ak66666/ThumbsUpUnsplitV9/Photos/IMG_20240110_212607524.jpg

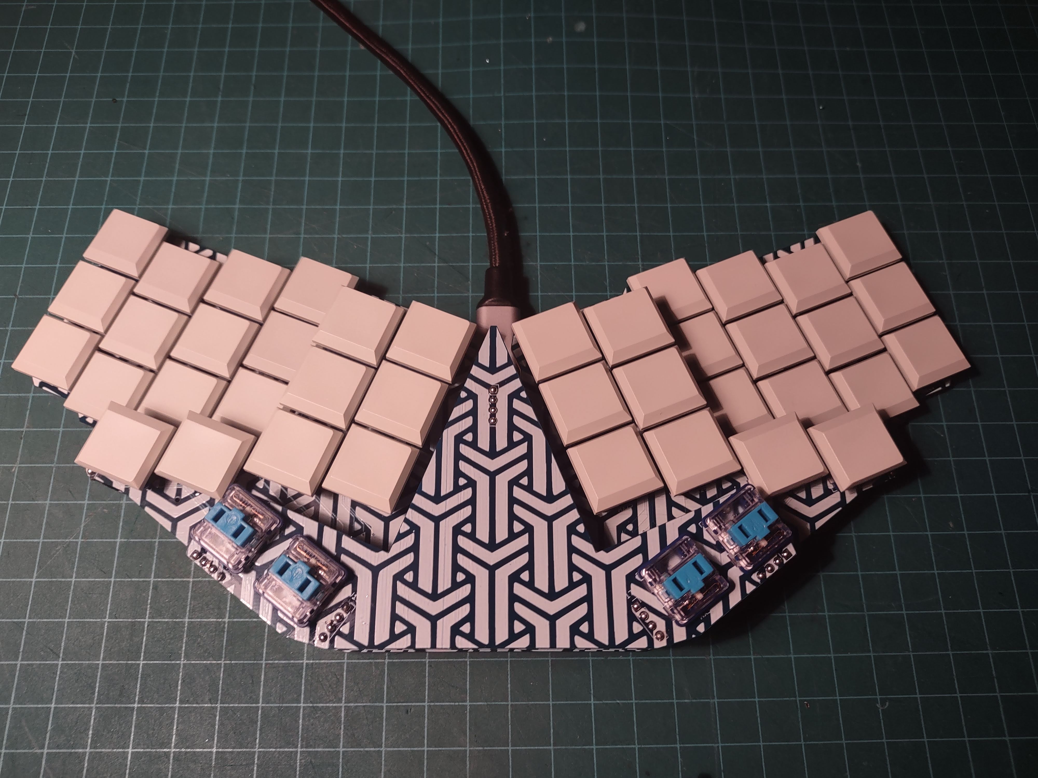
Photos/IMG_20240110_212607524.jpg
