ak66666/ThumbsUpUnsplitV9/Photos/IMG_20240110_212735549.jpg

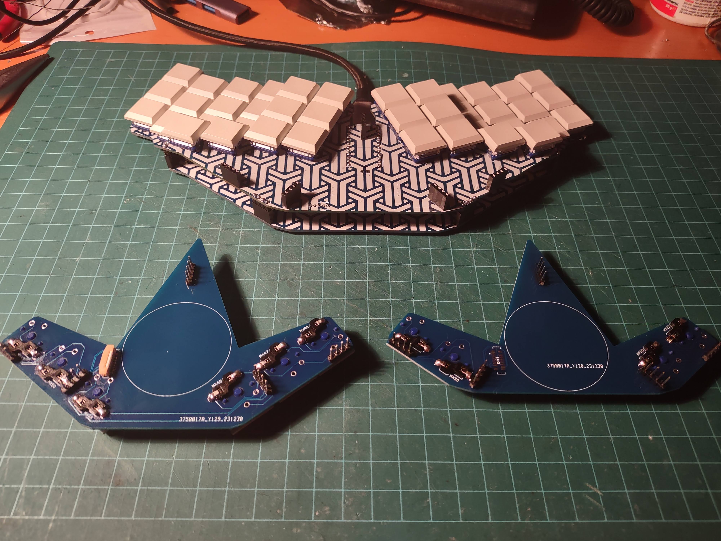
Photos/IMG_20240110_212735549.jpg
