ak66666/ThumbsUpUnsplitV9/Photos/IMG_20240110_212812123_HDR.jpg

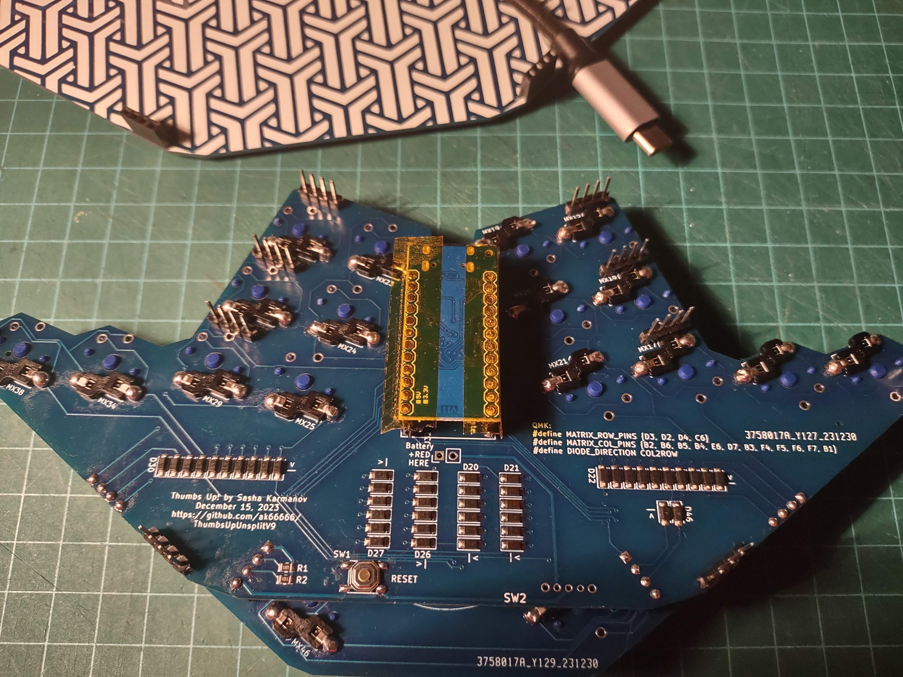
Photos/IMG_20240110_212812123_HDR.jpg
