ak66666/ThumbsUpUnsplitV9/Photos/IMG_20240110_213109584_HDR.jpg

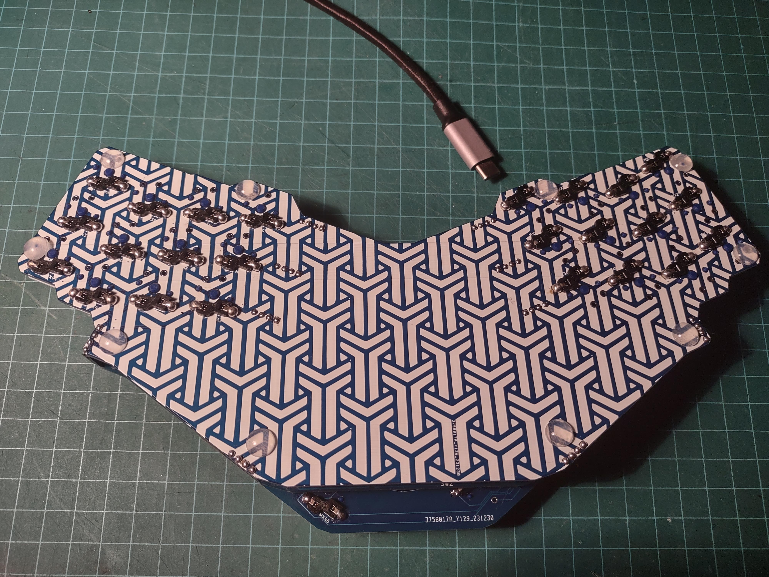
Photos/IMG_20240110_213109584_HDR.jpg
