ak66666/ThumbsUpUnsplitV9/Photos/IMG_20240401_145029431_HDR.jpg

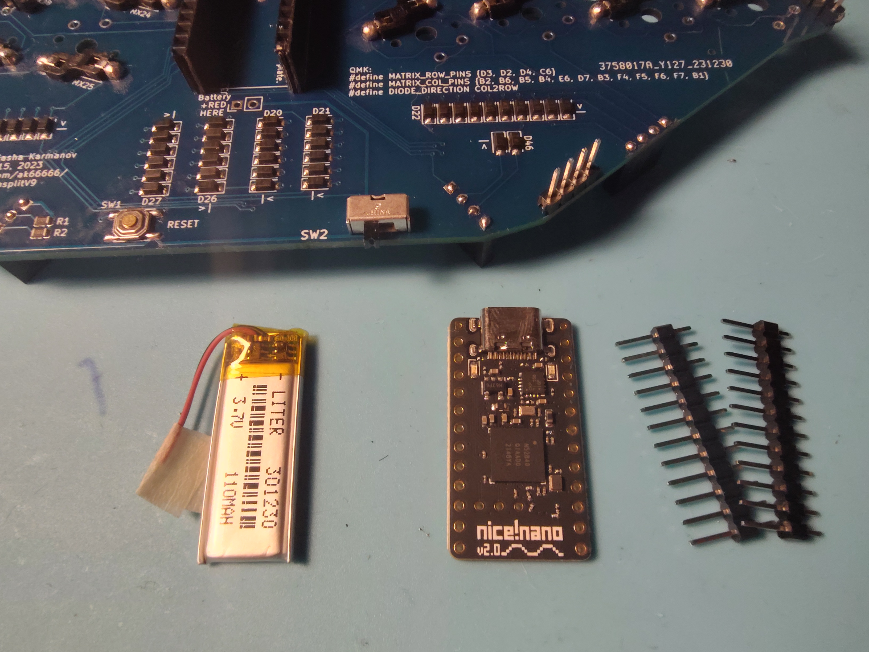
Photos/IMG_20240401_145029431_HDR.jpg
