ak66666/ThumbsUpUnsplitV9/Photos/IMG_20240401_145419424.jpg

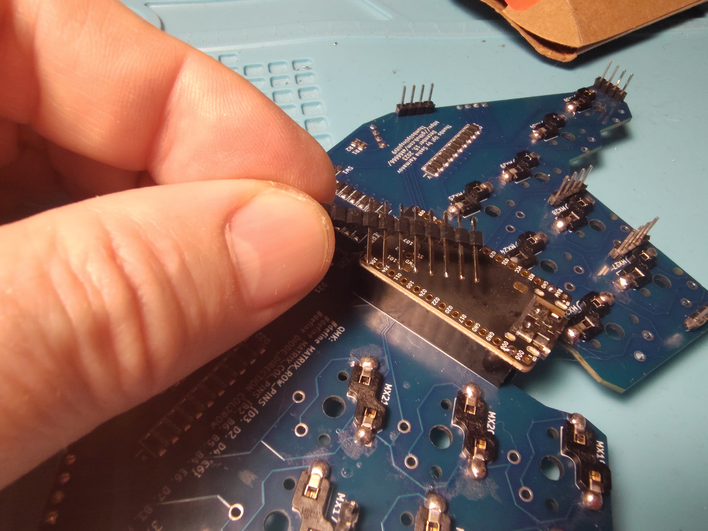
Photos/IMG_20240401_145419424.jpg
