ak66666/ThumbsUpUnsplitV9/Photos/IMG_20240401_145949781_HDR.jpg

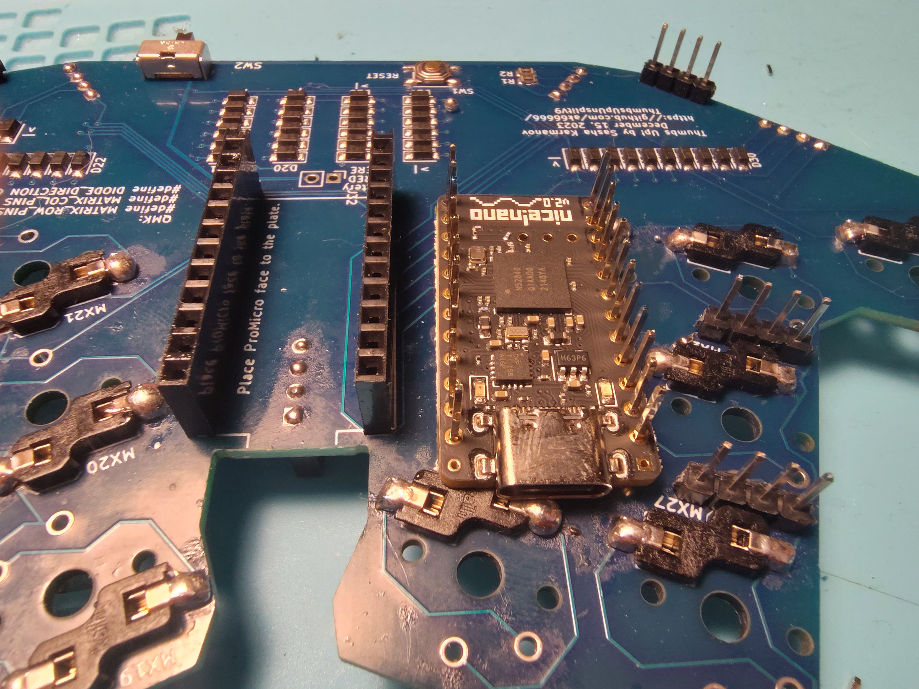
Photos/IMG_20240401_145949781_HDR.jpg
