ak66666/ThumbsUpUnsplitV9/Photos/IMG_20240401_150120789_HDR.jpg

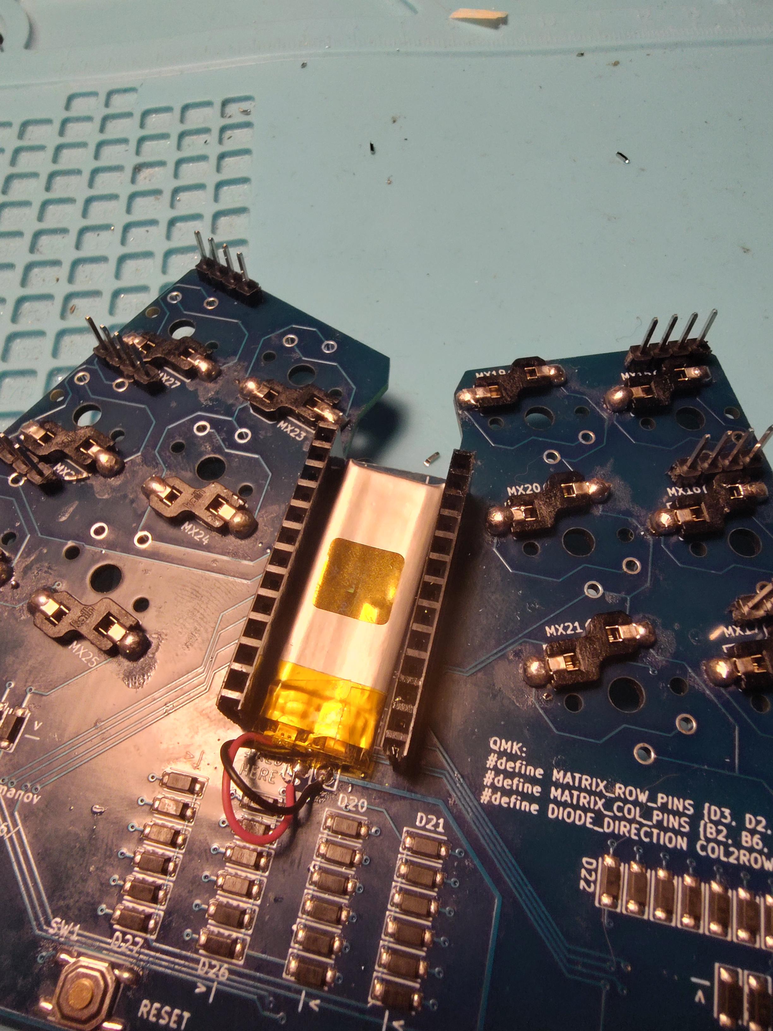
Photos/IMG_20240401_150120789_HDR.jpg
