ak66666/ThumbsUpUnsplitV9/Photos/IMG_20240401_150142731.jpg

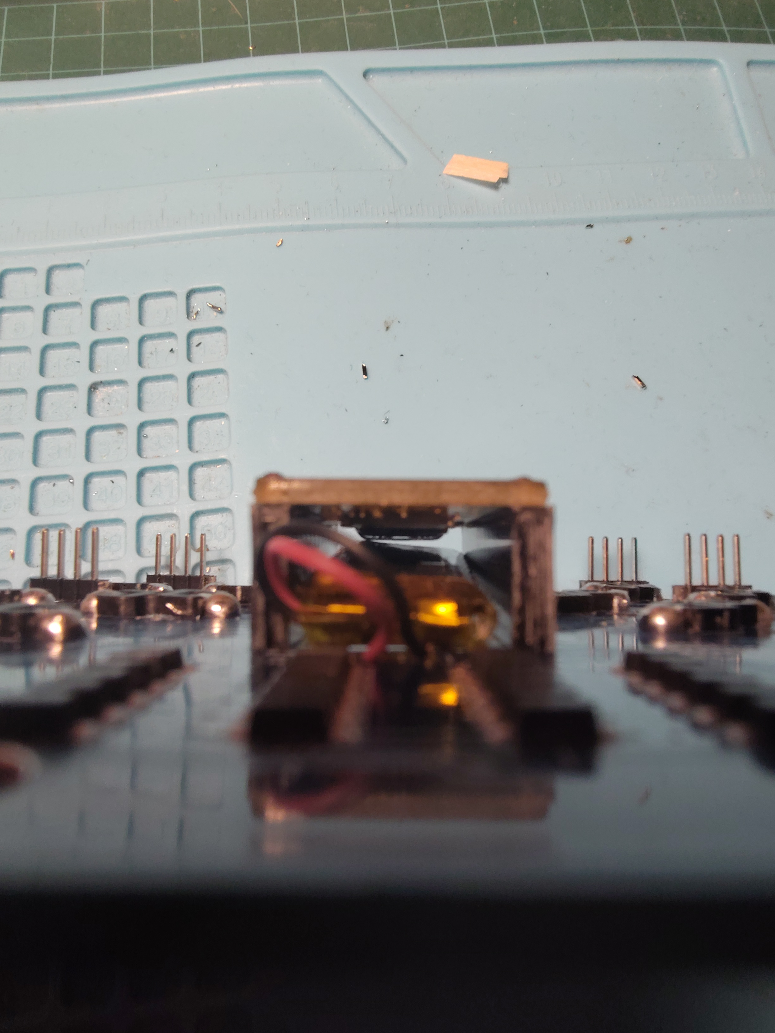
Photos/IMG_20240401_150142731.jpg
