ak66666/ThumbsUpUnsplitV9/Photos/IMG_20240401_223344100_HDR.jpg

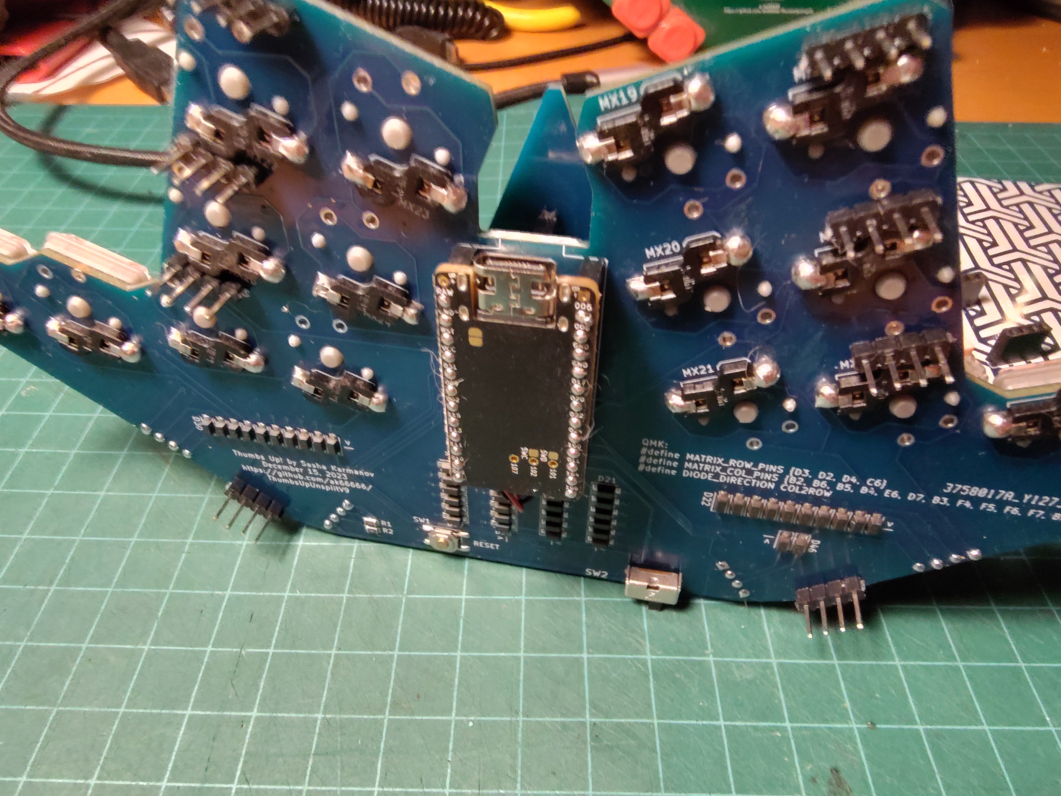
Photos/IMG_20240401_223344100_HDR.jpg
