ak66666/ThumbsUpUnsplitV9/Photos/IMG_20240401_223437867_HDR.jpg

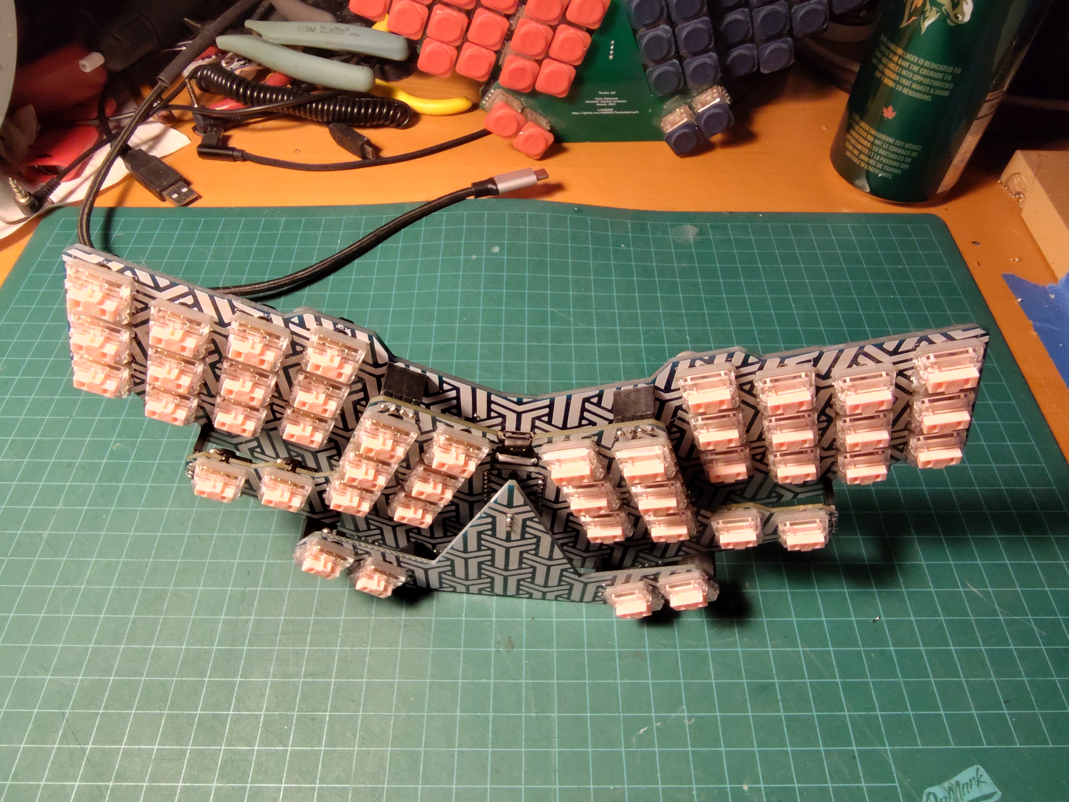
Photos/IMG_20240401_223437867_HDR.jpg
