ak66666/ThumbsUpUnsplitV9/Silkscreens/44 Key Keyboard Layout 20 pct.png

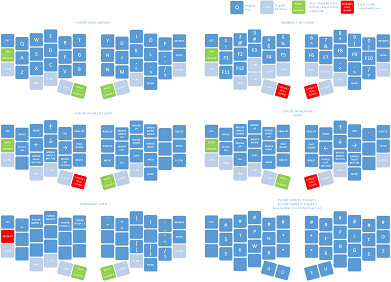
Silkscreens/44 Key Keyboard Layout 20 pct.png
