ak66666/ThumbsUpUnsplitV9/Silkscreens/Pattern.png

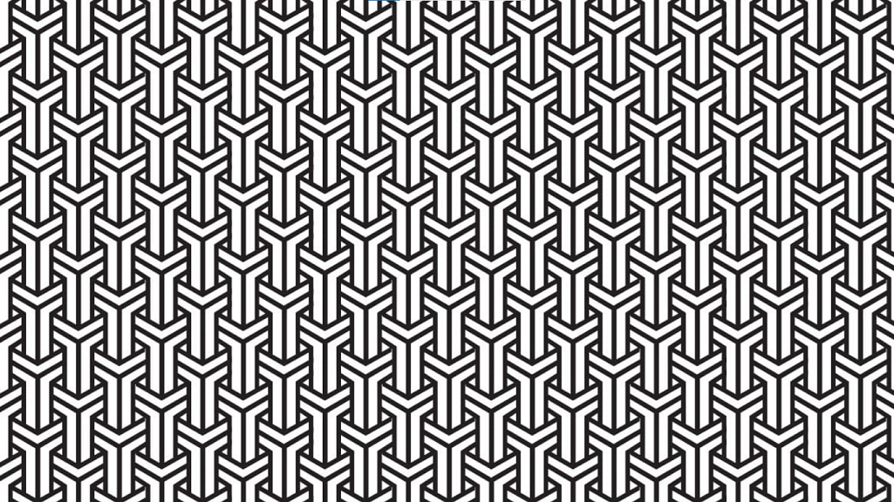
Silkscreens/Pattern.png
