ak66666/ThumbsUpUnsplitV9/Silkscreens/QWERTY.png

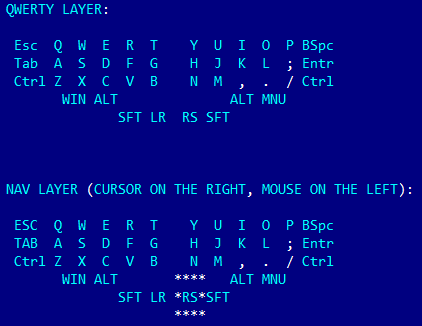
Silkscreens/QWERTY.png
